Clewsy/temp0/data/0.96-oled-module-dimensions.jpg

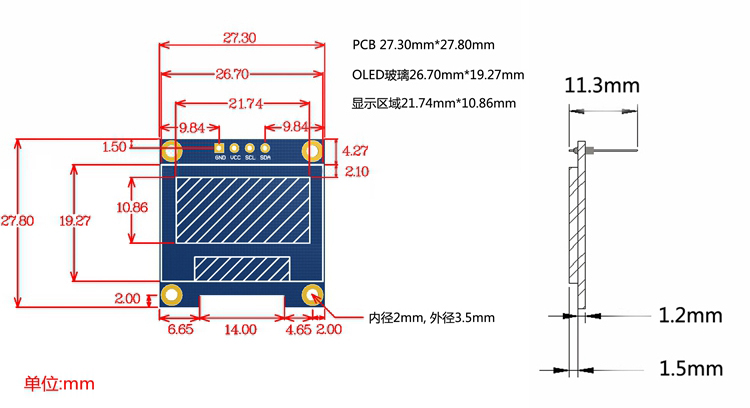
data/0.96-oled-module-dimensions.jpg
