Clewsy/temp0/data/pro_trinket_5V_pinout.jpeg

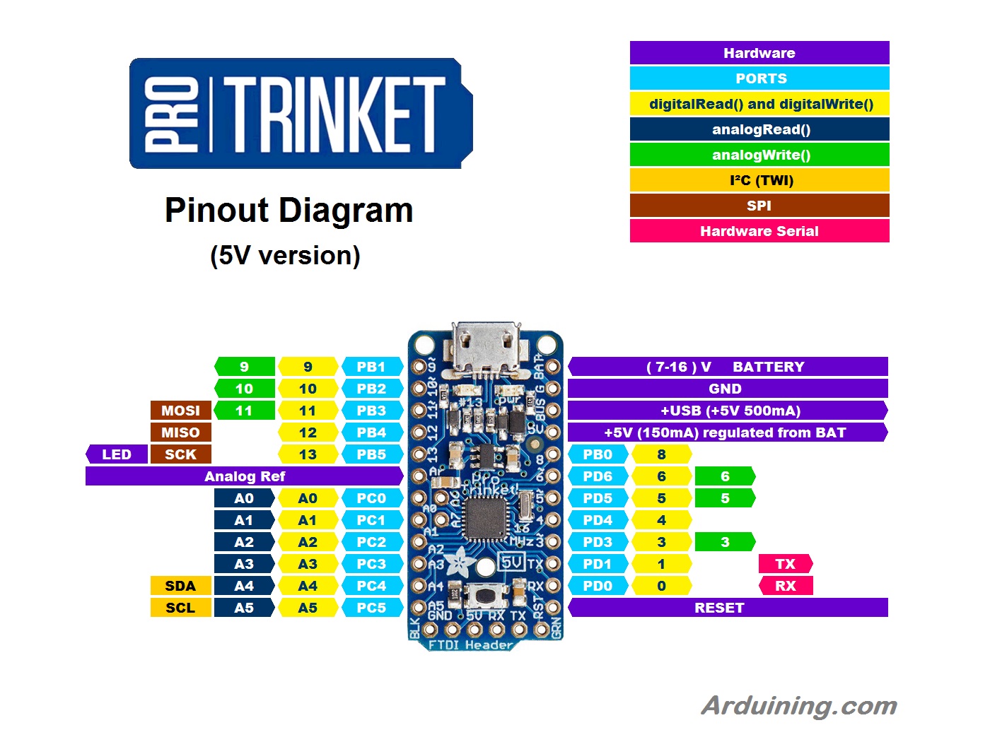
data/pro_trinket_5V_pinout.jpeg
