Clewsy/temp0/data/pro_trinket_dimensions_inches.png

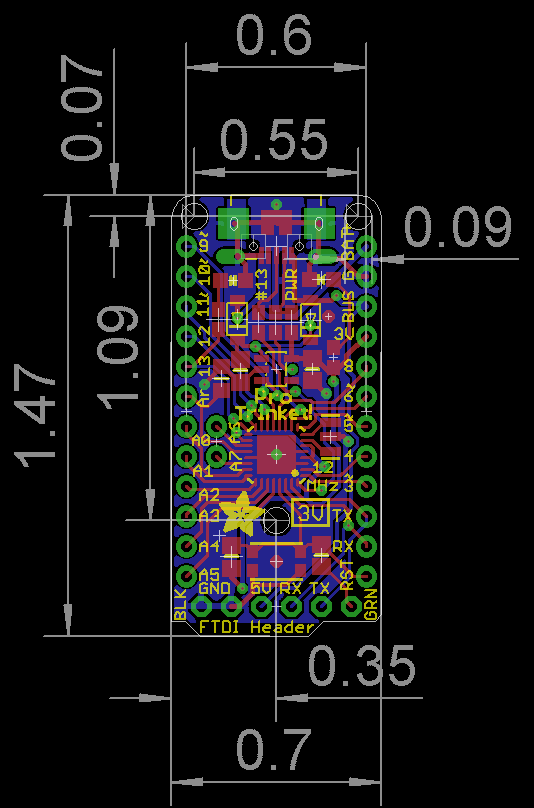
data/pro_trinket_dimensions_inches.png
